b-arnett/LoRaWeatherStation/SmartHouse/CAD/CHLid.3mf

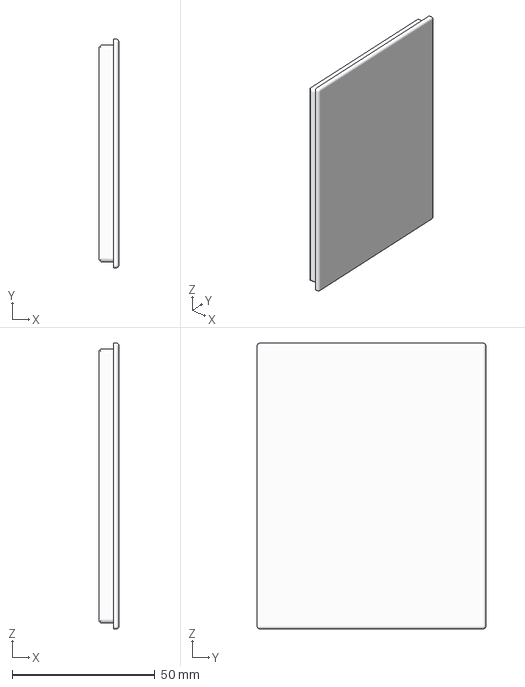
[picture p18: CAD file, 2025-05-18]
SmartHouse/CAD/CHLid.3mf
7.00 x 80.0 x 100.0 mm
